bwack/C64-Saver-bwack/oldfiles/C64 Saver 1/1.1-1.3/c64saver_bomcost.pdf

kalkyle

Side 1

BOM cost C64 Saver 1.2

elfa | pricex1 | tot | totx20pcs
1 | 16059765330k (100pcs+) | 0,2965 | 0,2965 | 5,93
1 | 30011792 TL431 (10pcs +) | 3,1 | 3,1 | 62
2 | 16044903 3k3 | 0,181875 | 0,36375 | 7,275
2 | 16044929 3k9 | 0,181875 | 0,36375 | 7,275
2 | 16044788 1k | 0,181875 | 0,36375 | 7,275
1 | 16045504 1M | 0,181875 | 0,181875 | 3,6375
1 | 17130776 BSS84 | 3,38 | 3,38 | 67,6
1 | 17137235 IRF9328PBF (10pcs+) | 5,01 | 5,01 | 100,2
1 | 11042198 red led 0603 | 3,22 | 3,22 | 64,4
1 | 17510287 green led 0603 | 2,56 | 2,56 | 51,2
0,13 | 11041696 kabel | 28,25 | 3,6725 | 73,45
other | 0
1 oshpark | pcb | 7,47 | 7,47 | 149,33
0,03khs03-1m | bk sleve 3.2mm-1.6mm | 15,19 | 0,4557 | 9,114
0,045ebay | sleeving transp | 17,71 | 0,79695 | 15,939
1 | 14224747 din 8 fem | 14,5 | 14,5 | 290
1 | 14226122 din 8 male | 12,63 | 12,63 | 252,6
1 | shipment? | 20 | 20 | 20
1 paypal | transfer | 9 | 9 | 9
subtot | 87,36 | 1196,23
ship | 45
tot | 45

200 NOK
