bwack/C64-Saver-bwack/oldfiles/C64 Saver 1/1.0/bomcost.pdf

kalkyle

Side 1

elfadistrelec part numbers

price | x6 | pricex6
1 65-754-82 | 100n | 0 | 6 | 0
1 30-011-792 | TL431 | 2,35 | 6 | 14,1
4 60-597-17 | 3k3 | 0,417 | 24 | 10,008
2 60-597-19 | 3k9 | 0,417 | 12 | 5,004
2 60-597-53 | 100k | 0,417 | 12 | 5,004
1 71-307-76 | BSS84 | 5,98 | 6 | 35,88
1 71-372-36 | FDS4435A | 11,8 | 6 | 70,8
1 75-310-18 | green | 1,42 | 6 | 8,52
1 75-310-19 | red | 2,32 | 6 | 13,92
1060-597-52 | 91k | 0 | 60 | 0
1060-597-55 | 120k | 0 | 60 | 0
1 oshpark | pcb | 9,45 | 6 | 56,7
1 elektroshop sleeving | 1,2397 | 6 | 7,4382
1 elektroshop din 7 fem | 10 | 6 | 60
1 elektroshop din 7 male | 10 | 6 | 60
1 | shipment? | 20 | 6 | 120
subtot | 75,8107 | 467,3742
ship | 45
tot | 120,8107

200 NOK
