bwack/C64-Saver-bwack/oldfiles/addon board 1.3/C64Saver2-addon.kicad_pcb_1_3.png

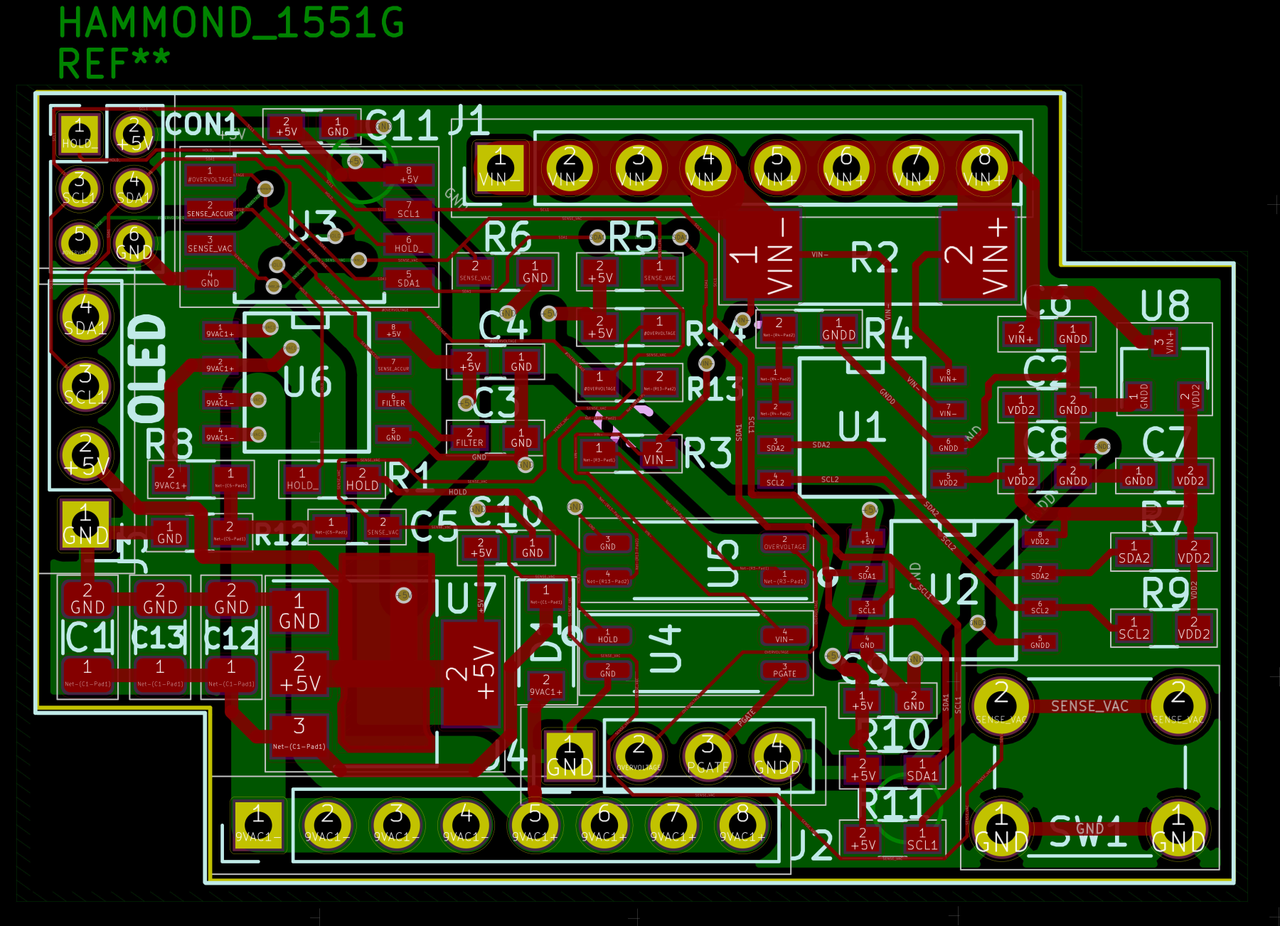
oldfiles/addon board 1.3/C64Saver2-addon.kicad_pcb_1_3.png
