bwack/C64-Saver-bwack/oldfiles/C64 Saver 1/1.1-1.3/eagleUp-export/eagleUp_c64saver_1.1_board_bottom.png

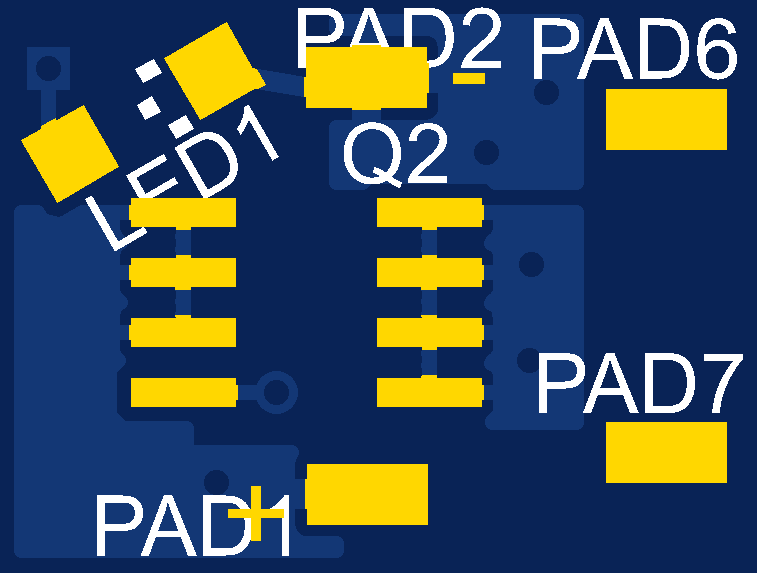
oldfiles/C64 Saver 1/1.1-1.3/eagleUp-export/eagleUp_c64saver_1.1_board_bottom.png
