bwack/C64-Saver-bwack/oldfiles/C64 Saver 1/1.1-1.3/sketchup/c64saver11_export2.jpg

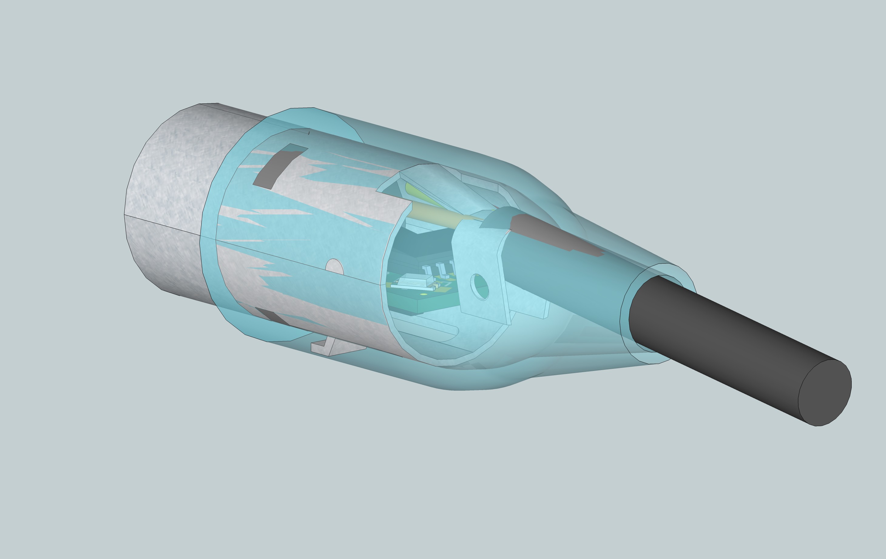
oldfiles/C64 Saver 1/1.1-1.3/sketchup/c64saver11_export2.jpg
