bwack/C64-Saver-bwack/oldfiles/C64 Saver SMD 2.5/C64Saver2_3D.png

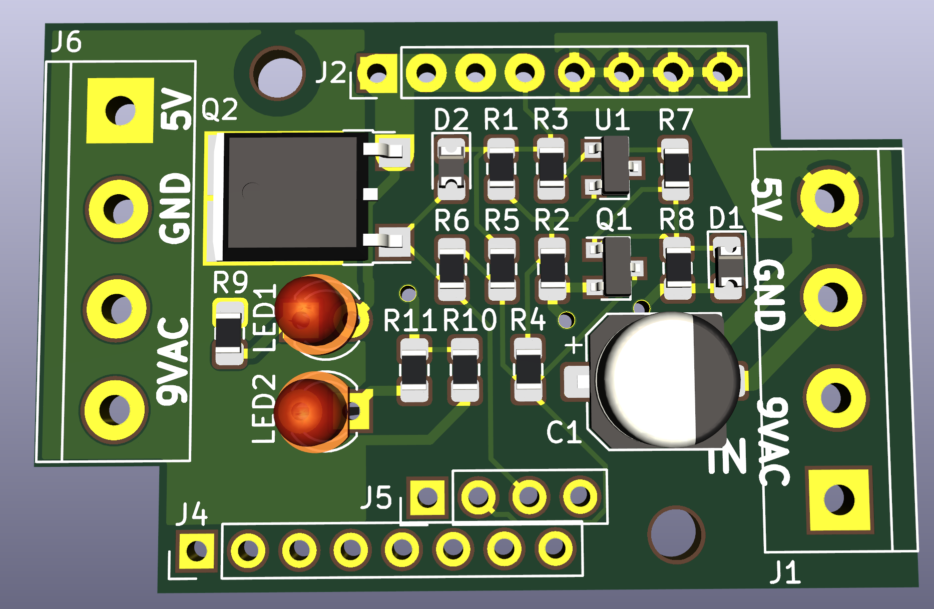
oldfiles/C64 Saver SMD 2.5/C64Saver2_3D.png
