bwack/C64-Saver-bwack/oldfiles/C64 Saver Throughhole 2.4/C64Saver2_3D_bottom.png

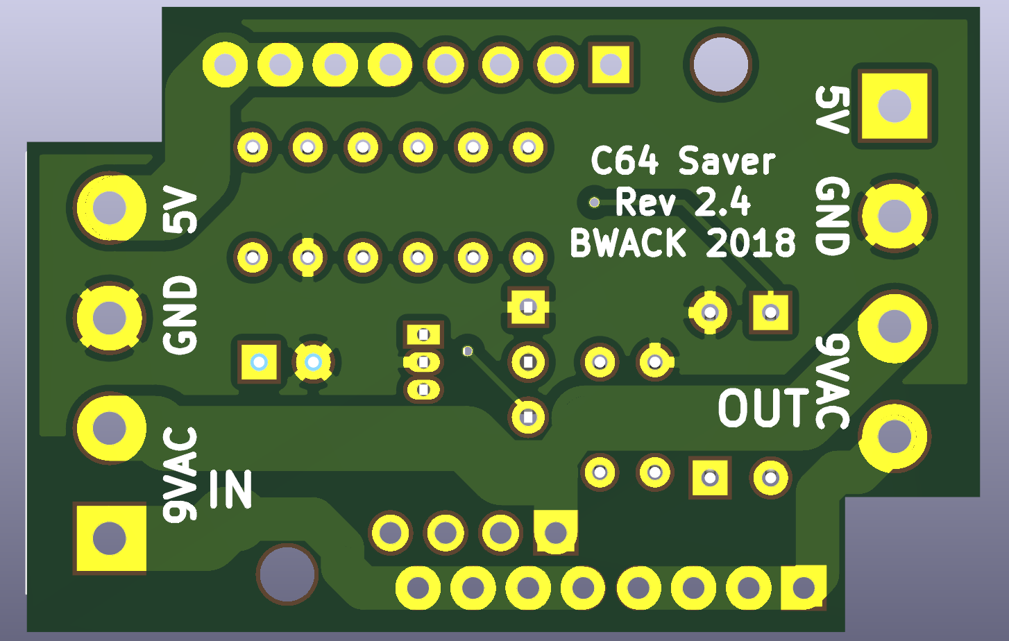
oldfiles/C64 Saver Throughhole 2.4/C64Saver2_3D_bottom.png
