bwack/C64-Saver-bwack/oldfiles/C64 Saver 1/1.1-1.3/eagleUp-export/C64Saverv1.1_wiring_a.jpg

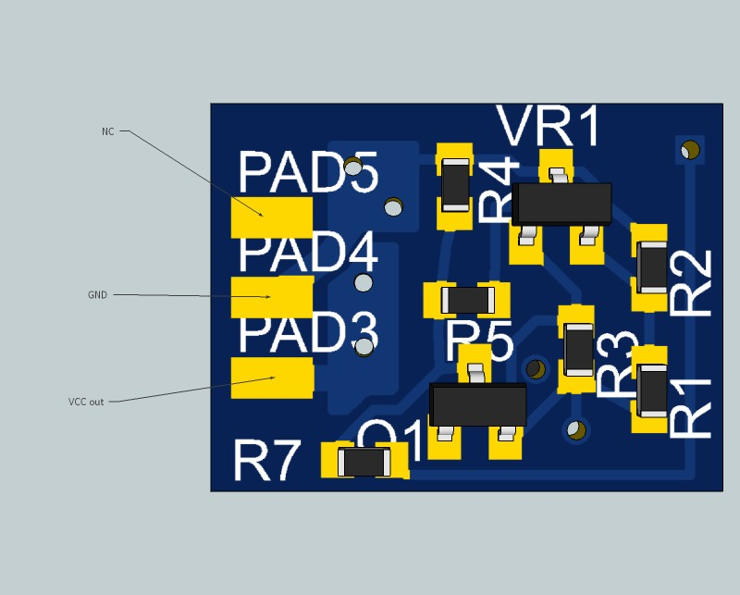
oldfiles/C64 Saver 1/1.1-1.3/eagleUp-export/C64Saverv1.1_wiring_a.jpg
