bwack/C64-Saver-bwack/oldfiles/C64 Saver 1/1.0/c64saver_v1.0_sch.pdf

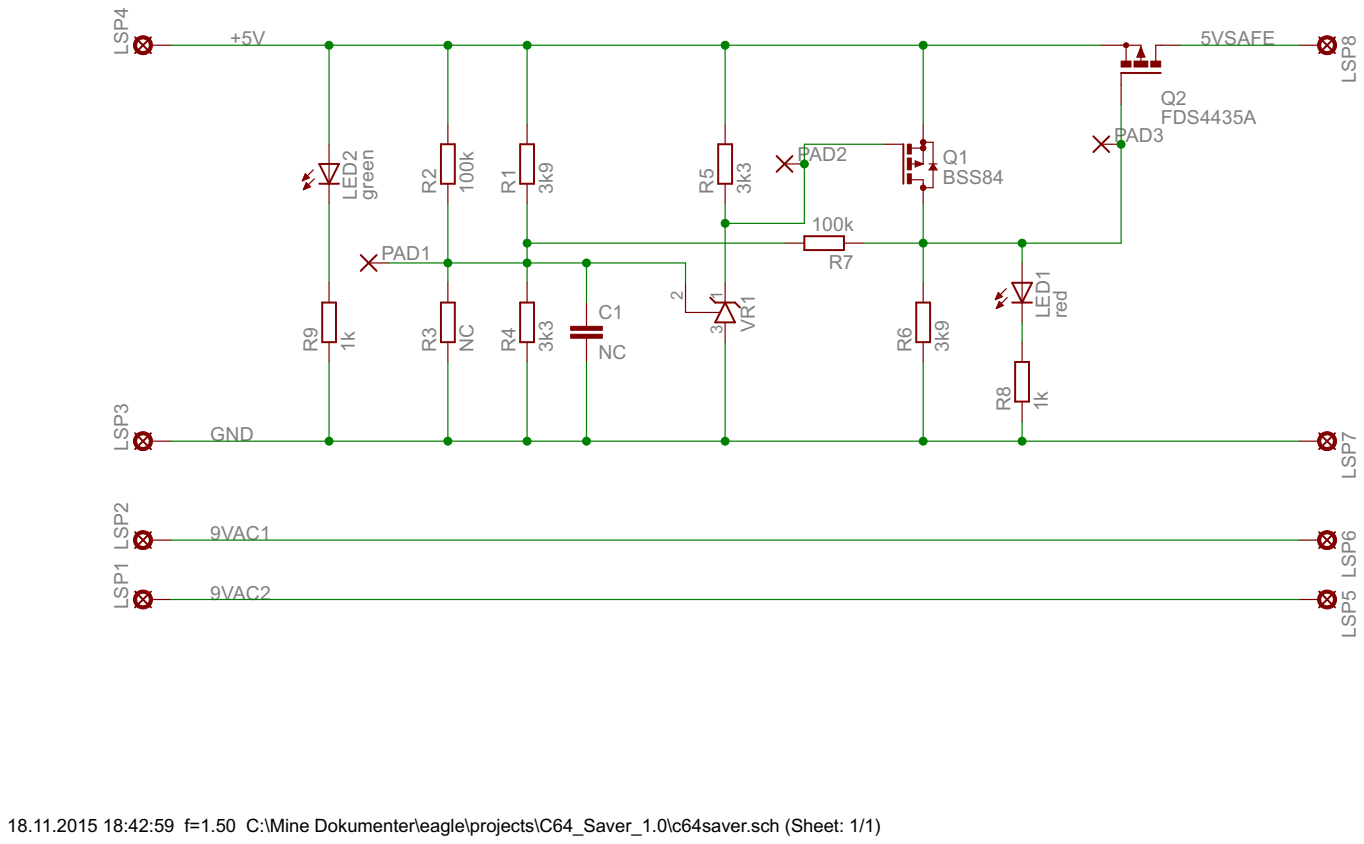
[picture p33: page 1]

18.11.2015 18:42:59 f=1.50 C:\Mine Dokumenter\eagle\projects\C64_Saver_1.0\c64saver.sch (Sheet: 1/1)
